adesandr/GliderThrow_Meter/docs/_decal/Decal.jpg

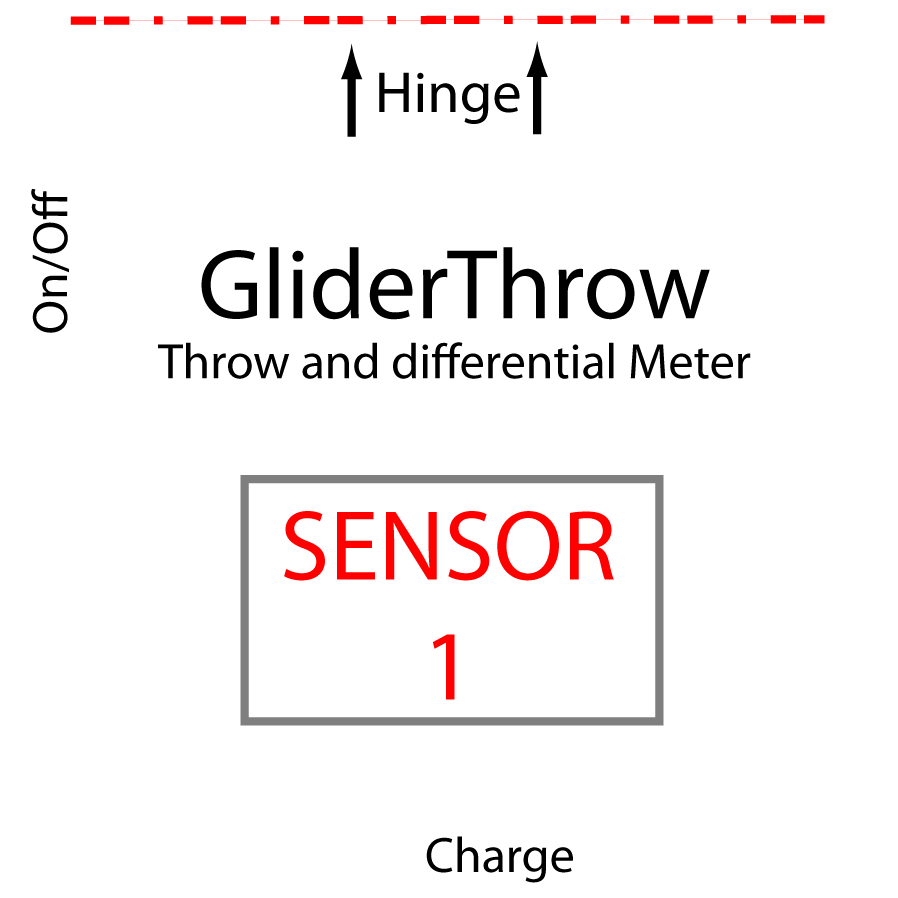
docs/_decal/Decal.jpg
