adesandr/GliderThrow_Meter/docs/_static/top-case-mount.JPG

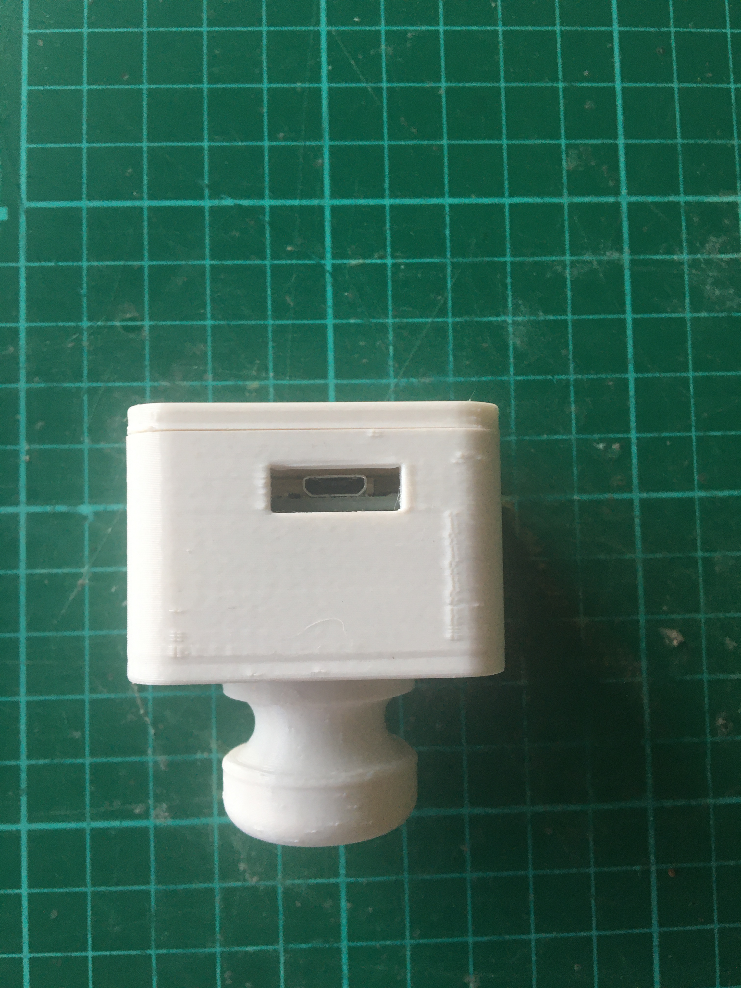
docs/_static/top-case-mount.JPG
